SmallCoral/wm8978/reports/pcb-review/2026-10-02-recheck-2347/bottom.png

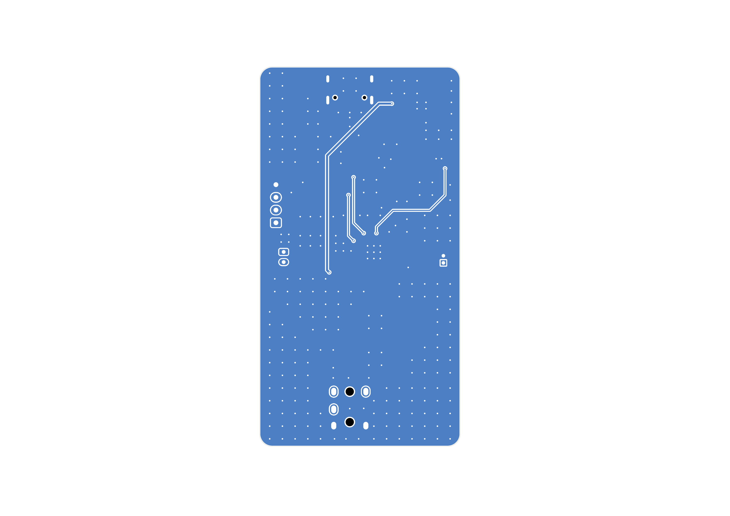
reports/pcb-review/2026-10-02-recheck-2347/bottom.png
